christian-kramer/GameVision-50-Re-Engineering/Images/20200601_104712.jpg

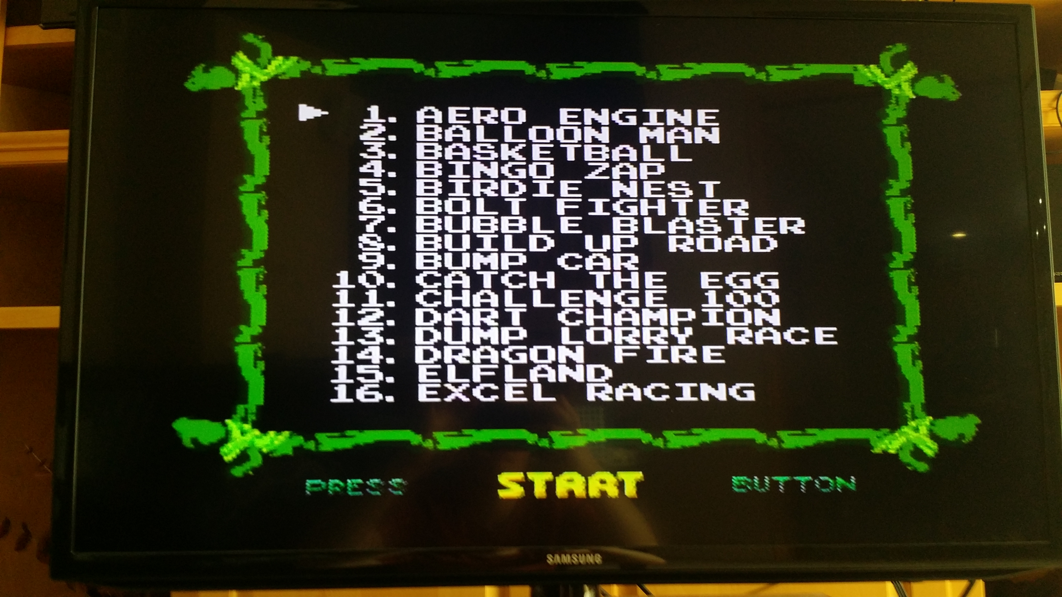
Images/20200601_104712.jpg
