christian-kramer/GameVision-50-Re-Engineering/Images/20200601_112329.jpg

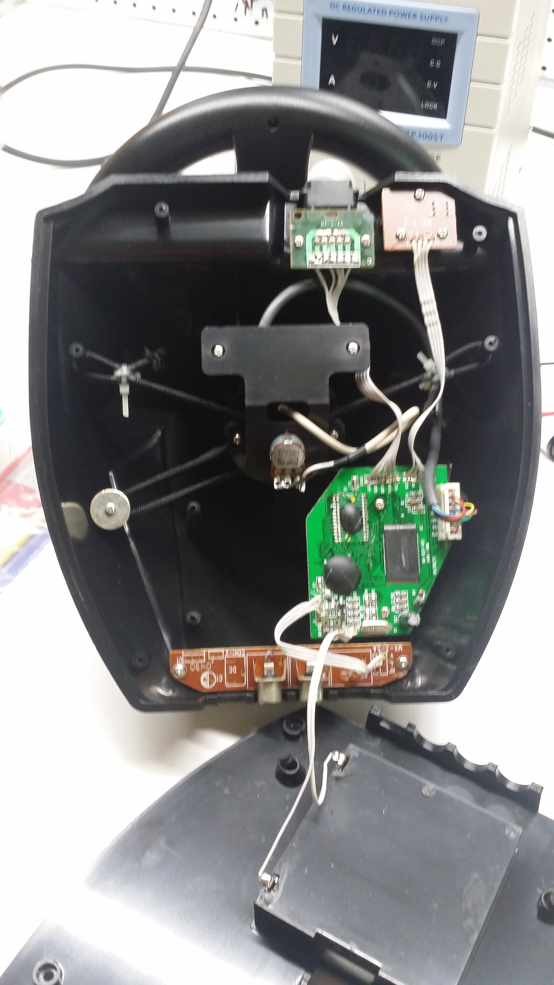
Images/20200601_112329.jpg
