christian-kramer/GameVision-50-Re-Engineering/Images/20200601_120232.jpg

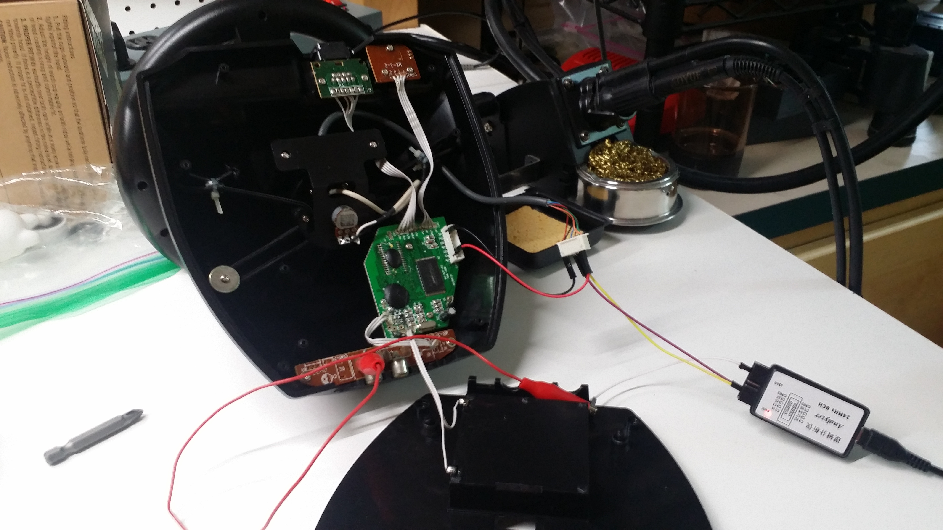
Images/20200601_120232.jpg
