christian-kramer/GameVision-50-Re-Engineering/Images/20200603_190824.jpg

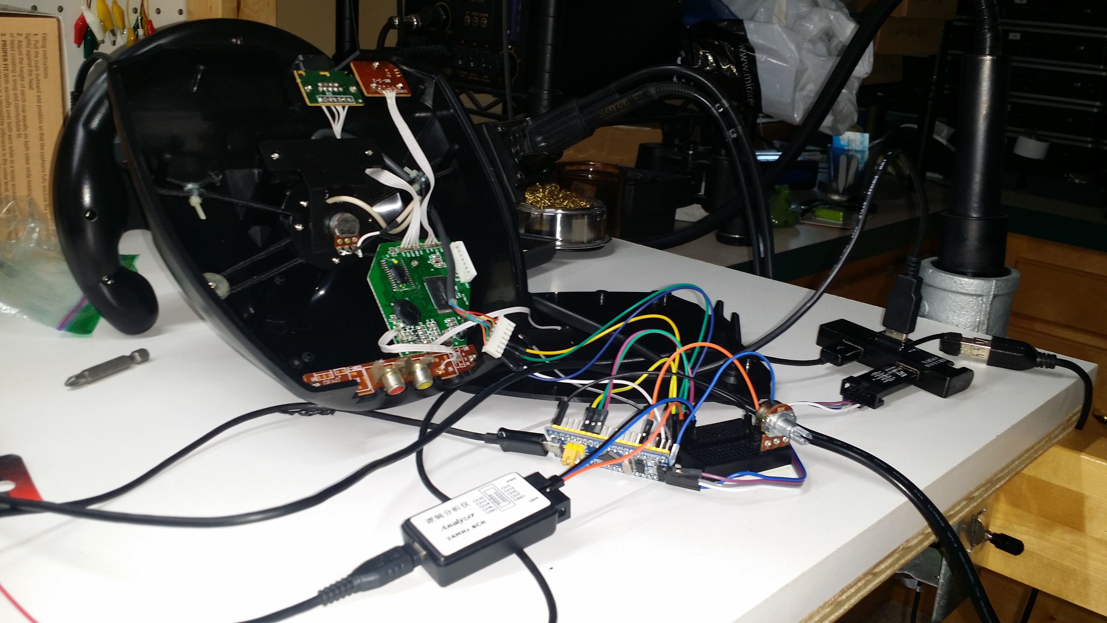
Images/20200603_190824.jpg
