christian-kramer/GameVision-50-Re-Engineering/Images/20200603_190827.jpg

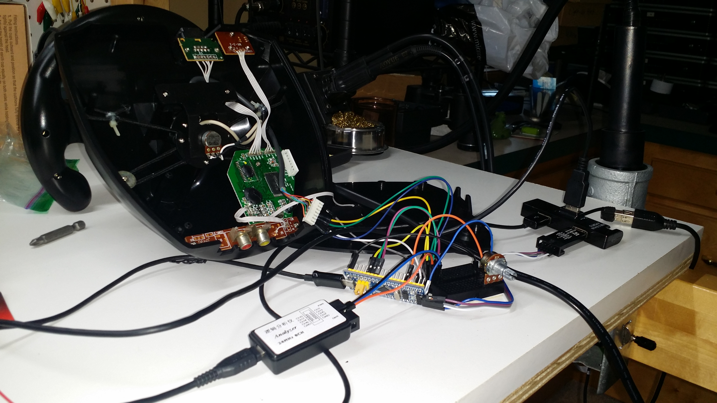
Images/20200603_190827.jpg
