christian-kramer/GameVision-50-Re-Engineering/Images/20200603_190832.jpg

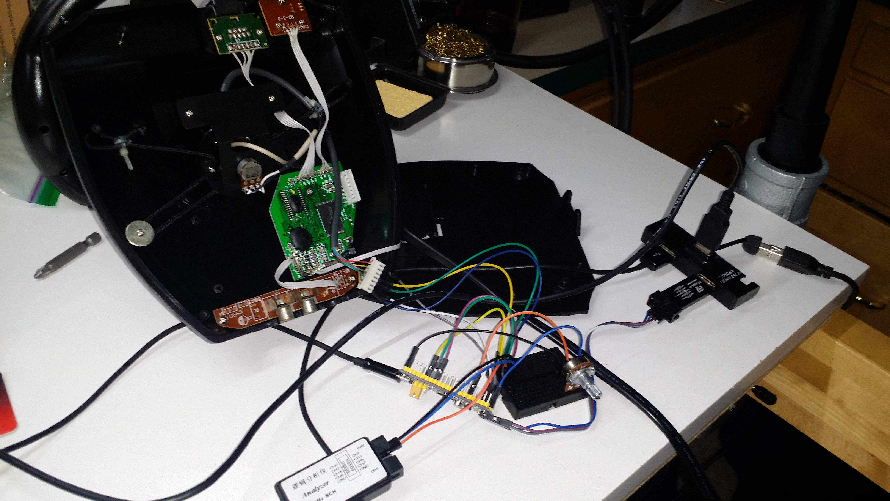
Images/20200603_190832.jpg
