christian-kramer/GameVision-50-Re-Engineering/Images/20200610_164020.jpg

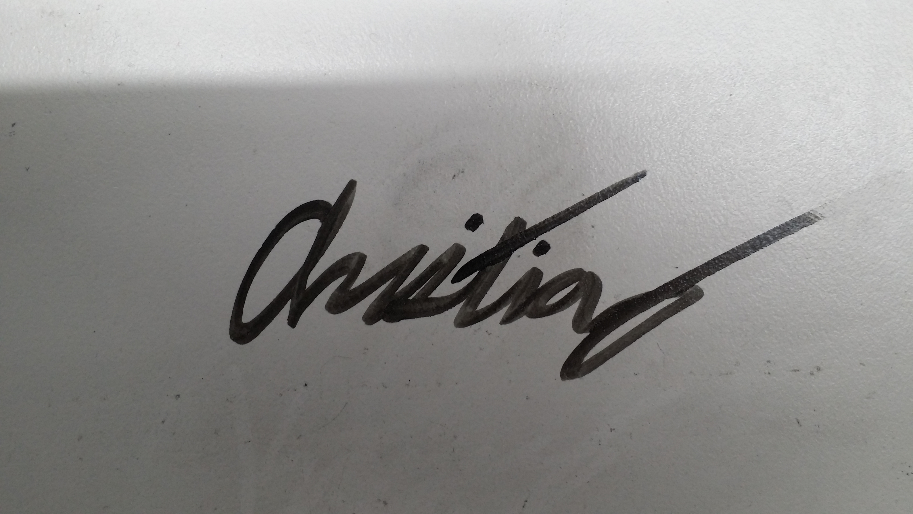
Images/20200610_164020.jpg
